septentrio-gnss/mowi/3Doutput/png_renders/mowi_angle_2.png

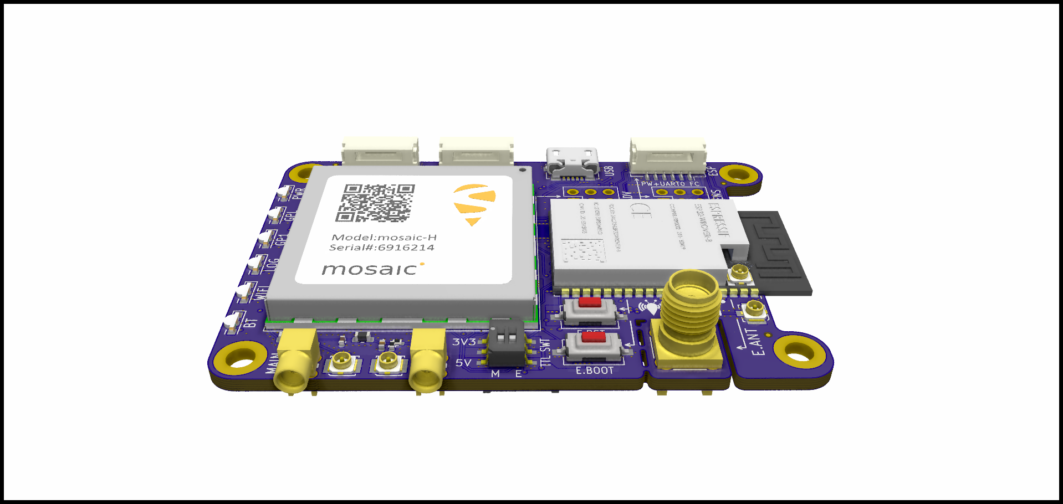
3Doutput/png_renders/mowi_angle_2.png
