septentrio-gnss/mowi/3Doutput/png_renders/mowi_angle_3.png

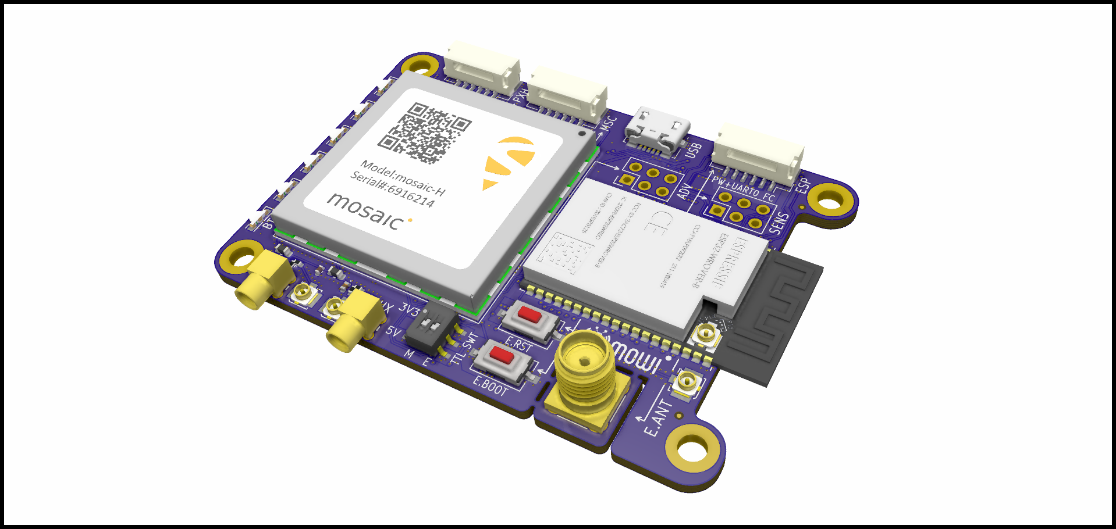
3Doutput/png_renders/mowi_angle_3.png
