septentrio-gnss/mowi/3Doutput/png_renders/mowi_angle_4.png

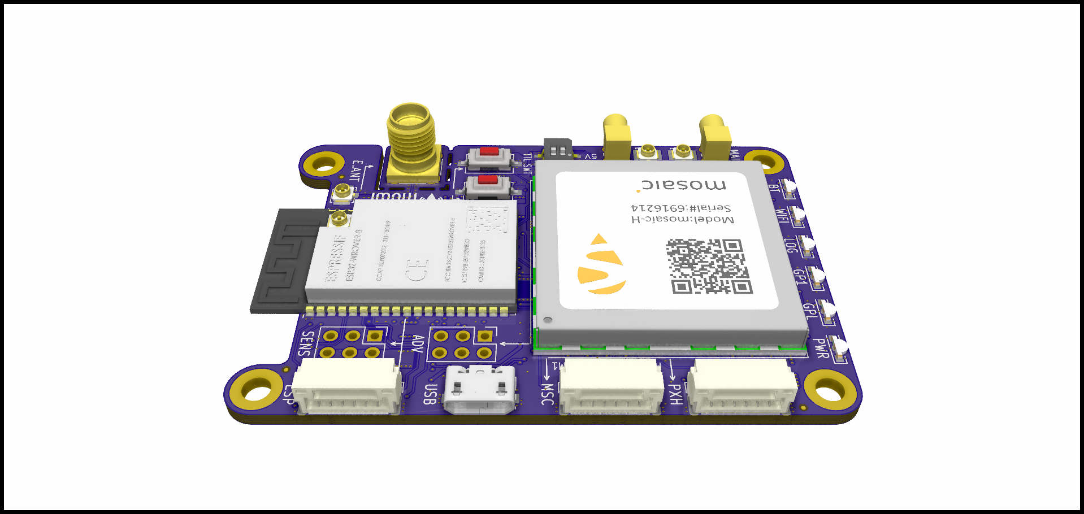
3Doutput/png_renders/mowi_angle_4.png
