septentrio-gnss/mowi/3Doutput/png_renders/mowi_bottom.png

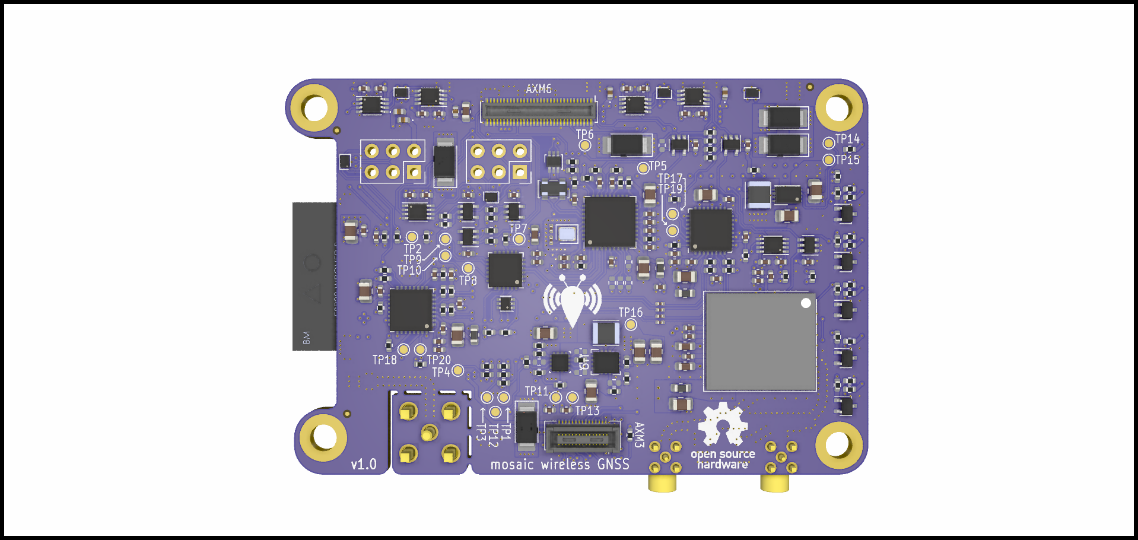
3Doutput/png_renders/mowi_bottom.png
