septentrio-gnss/mowi/readmeSource/examples_wifi_client_networks.png

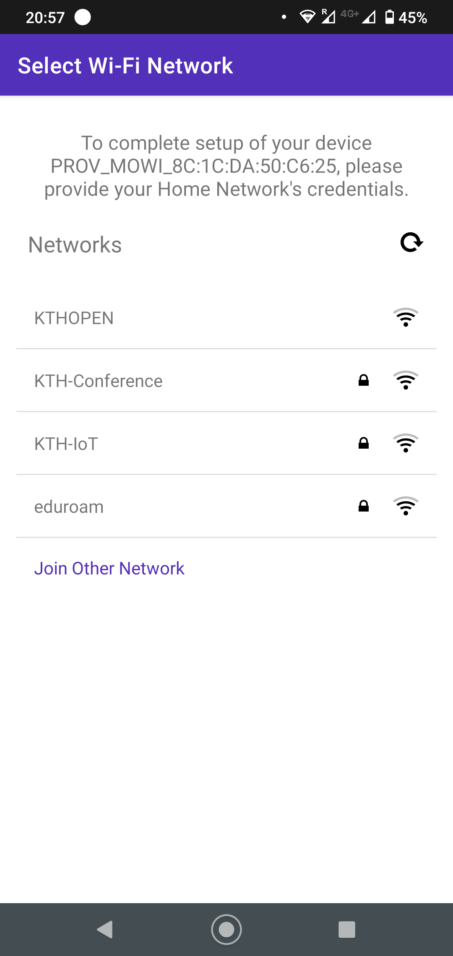
readmeSource/examples_wifi_client_networks.png
