septentrio-gnss/mowi/readmeSource/examples_wifi_client_search.png

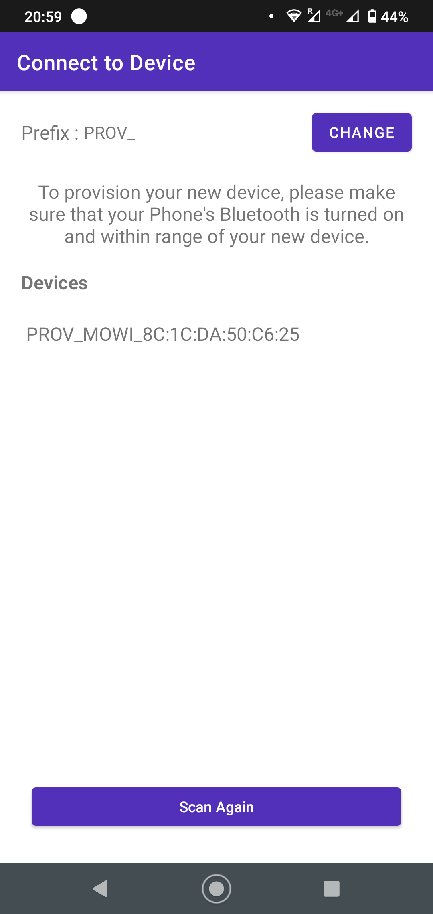
readmeSource/examples_wifi_client_search.png
