septentrio-gnss/mowi/readmeSource/mowi_3Drender_angle_3.png

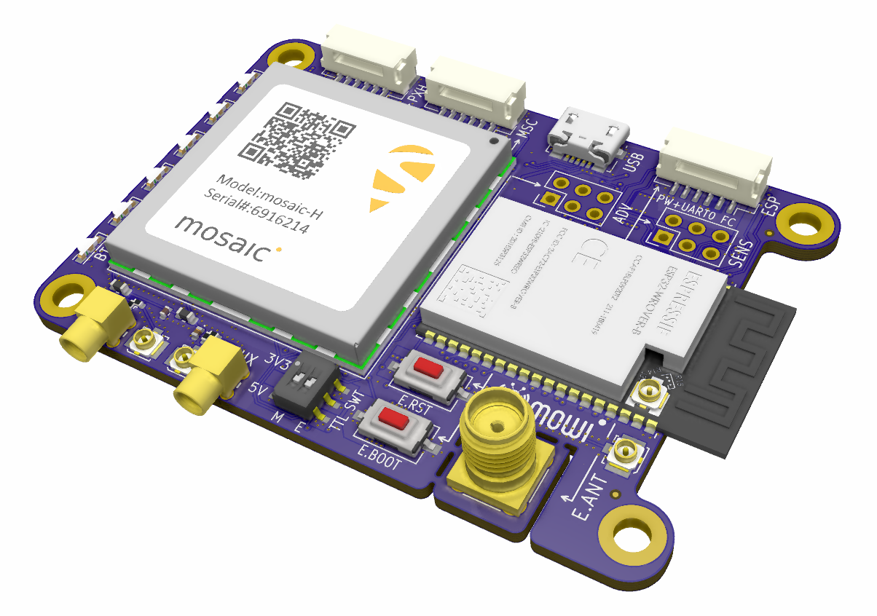
readmeSource/mowi_3Drender_angle_3.png
