septentrio-gnss/mowi/readmeSource/phone_mockup.png

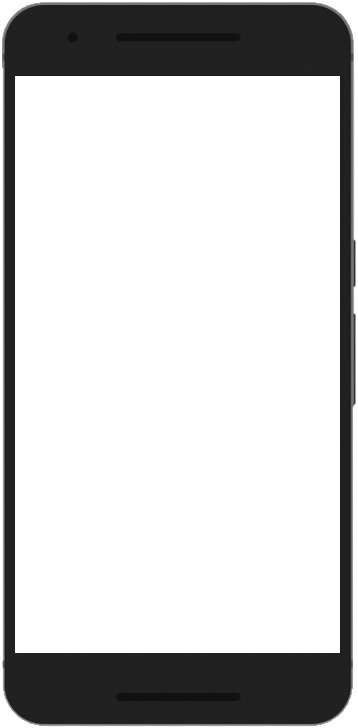
readmeSource/phone_mockup.png
