septentrio-gnss/mowi/mowi/mowi.sch

## KiCad design mowi/mowi.sch (2024-07-09)

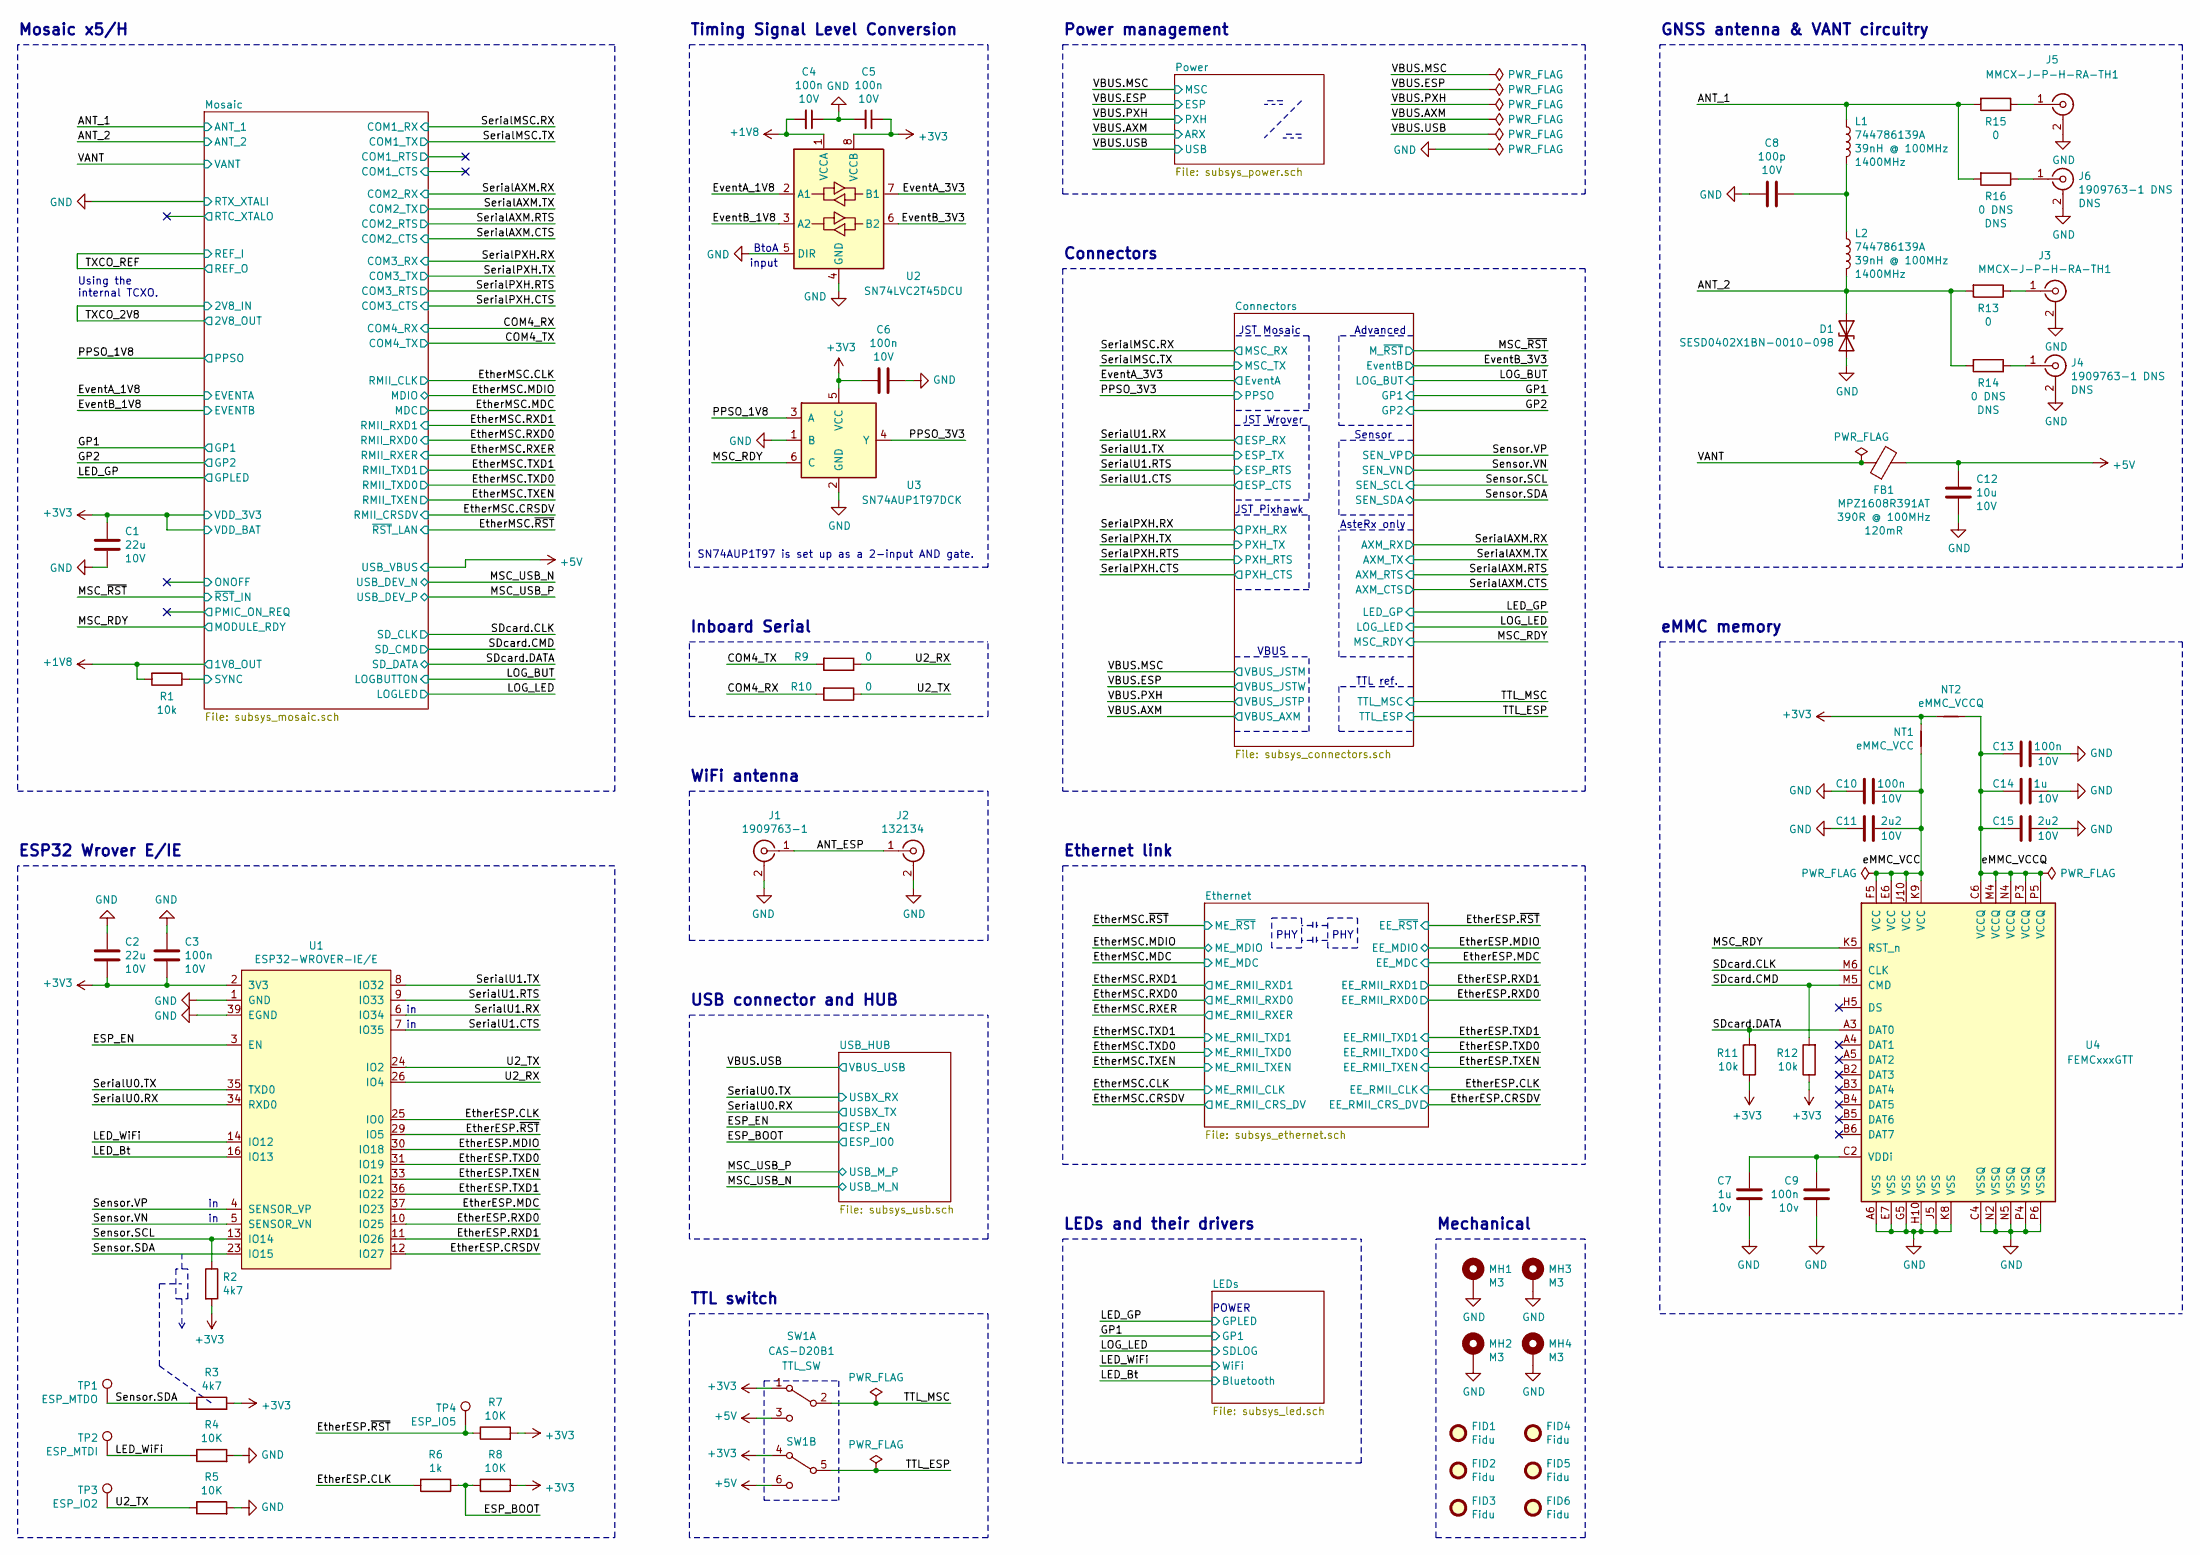
[picture p45: schematic mowi.sch]

Parts:
C1, C2: 22u; C_0805_2012Metric; Voltage 10V
C3, C4, C5, C6, C10, C13: 100n; C_0402_1005Metric; Voltage 10V
C7: 1u; C_0402_1005Metric; Voltage 10v
C8: 100p; C_0402_1005Metric; Voltage 10V
C9: 100n; C_0402_1005Metric; Voltage 10v
C11, C15: 2u2; C_0603_1608Metric; Voltage 10V
C12: 10u; C_0805_2012Metric; Voltage 10V
C14: 1u; C_0402_1005Metric; Voltage 10V
D1: SESD0402X1BN-0010-098; D_0402_1005Metric
FB1: MPZ1608R391AT; L_0603_1608Metric
FID1, FID2, FID3, FID4, FID5, FID6: Fidu; Fiducial_0.5mm_Mask1mm
J1: 1909763-1; TE_1909763-1
J2: 132134; SMA_Amphenol_132134-16_Vertical
J3, J5: MMCX-J-P-H-RA-TH1; Samtec_MMCX-J-P-H-RA-TH1
J4, J6: 1909763-1 DNS; TE_1909763-1
L1, L2: 744786139A; L_0603_1608Metric
MH1, MH2, MH3, MH4: M3; MountingHole_3.2mm_M3_ISO7380_Pad
NT1: eMMC_VCC; NetTie-2_SMD_Pad0.5mm
NT2: eMMC_VCCQ; NetTie-2_SMD_Pad0.5mm
R1, R11, R12: 10k; R_0402_1005Metric
R2, R3: 4k7; R_0402_1005Metric
R4, R5, R7, R8: 10K; R_0402_1005Metric
R6: 1k; R_0402_1005Metric
R9, R10, R13, R15: 0; R_0402_1005Metric
R14, R16: 0 DNS; R_0402_1005Metric
SW1: CAS-D20B1; SW_DIP_SPDTx02_CAS_CAS-D20B1_5.4x3.9x2.5mm
TP1: ESP_MTDO; TestPoint_Pad_D1.0mm
TP2: ESP_MTDI; TestPoint_Pad_D1.0mm
TP3: ESP_IO2; TestPoint_Pad_D1.0mm
TP4: ESP_IO5; TestPoint_Pad_D1.0mm
U1: ESP32-WROVER-IE/E; Esp_ESP32-WROVER-(I)E_18.0x31.4x3.3mm
U2: SN74LVC2T45DCU; VSSOP-8_2.3x2mm_P0.5mm
U3: SN74AUP1T97DCK; SOT-363_SC-70-6
U4: FEMCxxxGTT; FBGA-153_13.0x11.5x1.0mm

Connections:
+1V8: C4.2, R1.2, U2.1 (VCCA)
+3V3: C1.2, C2.2, C3.2, C5.1, C6.2, NT1.1, NT2.1, R2.2, R3.2, R7.2, R8.2, R11.1, R12.1, SW1.1 (A), SW1.4 (A), U1.2 (3V3), U2.8 (VCCB), U3.5 (VCC)
+5V: C12.2, FB1.2, SW1.3 (C), SW1.6 (C)
ANT_1: L1.1, R15.2, R16.2
ANT_2: D1.1 (A1), L2.2, R13.2, R14.2
ANT_ESP: J1.1 (In), J2.1 (In)
COM4_RX: R10.2
COM4_TX: R9.2
ESP_BOOT: R6.1, R8.1
ESP_EN: U1.3 (EN)
EtherESP.CLK: R6.2, U1.25 (IO0)
EtherESP.CRSDV: U1.12 (IO27)
EtherESP.MDC: U1.37 (IO23)
EtherESP.MDIO: U1.30 (IO18)
EtherESP.RXD0: U1.10 (IO25)
EtherESP.RXD1: U1.11 (IO26)
EtherESP.TXD0: U1.31 (IO19)
EtherESP.TXD1: U1.36 (IO22)
EtherESP.TXEN: U1.33 (IO21)
EtherESP.~RST: R7.1, TP4.1, U1.29 (IO5)
EventA_1V8: U2.2 (A1)
EventA_3V3: U2.7 (B1)
EventB_1V8: U2.3 (A2)
EventB_3V3: U2.6 (B2)
GND: C1.1, C2.1, C3.1, C4.1, C5.2, C6.1, C7.2, C8.2, C9.2, C10.2, C11.2, C12.1, C13.2, C14.2, C15.2, D1.2 (A2), J1.2 (Ext), J2.2 (Ext), J3.2 (Ext), J4.2 (Ext), J5.2 (Ext), J6.2 (Ext), MH1.1, MH2.1, MH3.1, MH4.1, R4.2, R5.2, U1.1 (GND), U1.15 (GND), U1.38 (GND), U1.39 (EGND), U2.4 (GND), U2.5 (DIR), U3.1 (B), U3.2 (GND), U4.A6 (VSS), U4.C4 (VSSQ), U4.E7 (VSS), U4.G5 (VSS), U4.H10 (VSS), U4.J5 (VSS), U4.K8 (VSS), U4.N2 (VSSQ), U4.N5 (VSSQ), U4.P4 (VSSQ), U4.P6 (VSSQ)
LED_Bt: U1.16 (IO13)
LED_WiFi: R4.1, TP2.1, U1.14 (IO12)
MSC_RDY: U3.6 (C), U4.K5 (RST_n)
unnamed: C7.1, C9.1, U4.C2 (VDDi)
unnamed: C8.1, L1.2, L2.1
unnamed: J3.1 (In), R13.1
unnamed: J4.1 (In), R14.1
unnamed: J5.1 (In), R15.1
unnamed: J6.1 (In), R16.1
PPSO_1V8: U3.3 (A)
PPSO_3V3: U3.4 (Y)
SDcard.CLK: U4.M6 (CLK)
SDcard.CMD: R12.2, U4.M5 (CMD)
SDcard.DATA: R11.2, U4.A3 (DAT0)
SYNC: R1.1
Sensor.SCL: R2.1, U1.13 (IO14)
Sensor.SDA: R3.1, TP1.1, U1.23 (IO15)
Sensor.VN: U1.5 (SENSOR_VN)
Sensor.VP: U1.4 (SENSOR_VP)
SerialU0.RX: U1.34 (RXD0)
SerialU0.TX: U1.35 (TXD0)
SerialU1.CTS: U1.7 (IO35)
SerialU1.RTS: U1.9 (IO33)
SerialU1.RX: U1.6 (IO34)
SerialU1.TX: U1.8 (IO32)
TTL_ESP: SW1.5 (B)
TTL_MSC: SW1.2 (B)
U2_RX: R9.1, U1.26 (IO4)
U2_TX: R5.1, R10.1, TP3.1, U1.24 (IO2)
VANT: FB1.1
eMMC_VCC: C10.1, C11.1, NT1.2, U4.E6 (VCC), U4.F5 (VCC), U4.J10 (VCC), U4.K9 (VCC)
eMMC_VCCQ: C13.1, C14.1, C15.1, NT2.2, U4.C6 (VCCQ), U4.M4 (VCCQ), U4.N4 (VCCQ), U4.P3 (VCCQ), U4.P5 (VCCQ)

Notes on the sheet:
ESP32 Wrover E/IE
TTL switch
GNSS antenna & VANT circuitry
POWER
LEDs and their drivers
Mechanical
Using the internal TCXO.
Mosaic x5/H
eMMC memory
BtoA
input
USB connector and HUB
SN74AUP1T97 is set up as a 2-input AND gate.
Timing Signal Level Conversion
Inboard Serial
Power management
AsteRx only
TTL ref.
Sensor
JST Pixhawk
JST Wrover
VBUS
Advanced
JST Mosaic
Connectors
PHY
Ethernet link
WiFi antenna
