septentrio-gnss/mowi/mowi/subsys_connectors.sch

## KiCad design mowi/subsys_connectors.sch (2021-09-02)

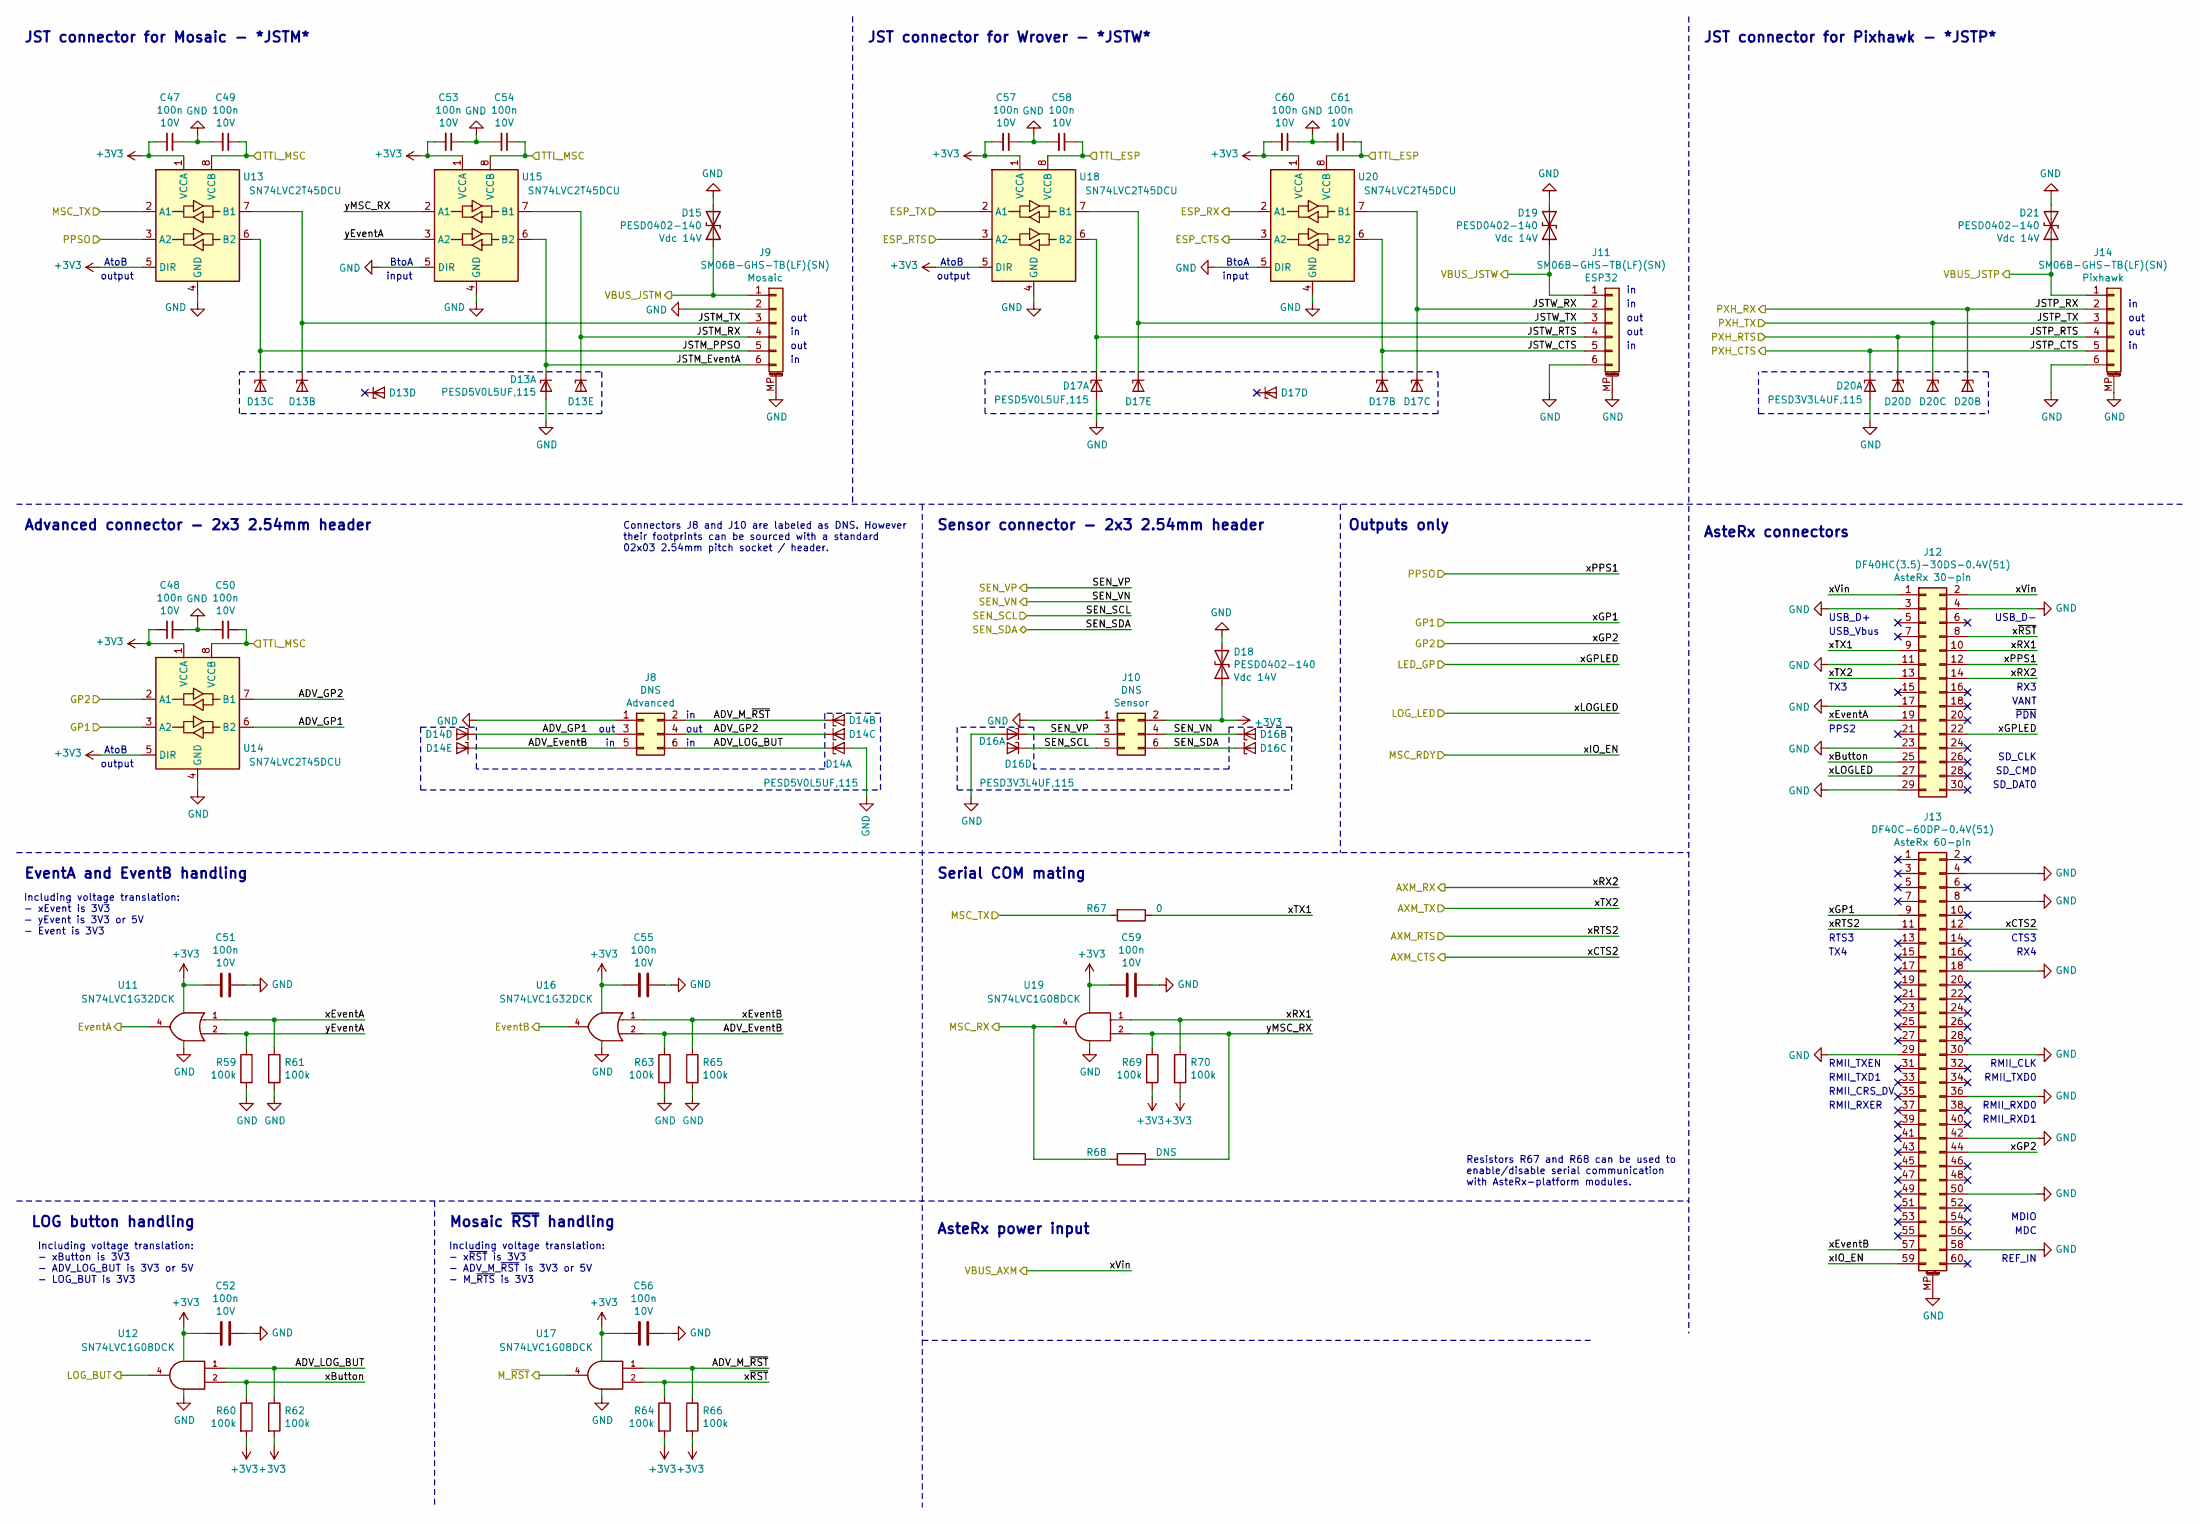
[picture p46: schematic subsys_connectors.sch]

Parts:
C47, C48, C49, C50, C51, C52, C53, C54, C55, C56, C57, C58, C59, C60, C61: 100n; C_0402_1005Metric; Voltage 10V
D13, D14, D17: PESD5V0L5UF,115; SOT-886
D15, D18, D19, D21: PESD0402-140; D_0402_1005Metric
D16, D20: PESD3V3L4UF,115; SOT-886
J8, J10: DNS; PinHeader_2x03_P2.54mm
J9, J11, J14: SM06B-GHS-TB(LF)(SN); JST_GH_SM06B-GHS-TB_1x06-1MP_P1.25mm_Horizontal
J12: DF40HC(3.5)-30DS-0.4V(51); Hirose_DF40HC-30DS-0.4V(51)
J13: DF40C-60DP-0.4V(51); Hirose_DF40C-60DP-0.4V(51)
R59, R60, R61, R62, R63, R64, R65, R66, R69, R70: 100k; R_0402_1005Metric
R67: 0; R_0402_1005Metric
R68: DNS; R_0402_1005Metric
U11, U16: SN74LVC1G32DCK; SOT-353_SC-70-5
U12, U17, U19: SN74LVC1G08DCK; SOT-353_SC-70-5
U13, U14, U15, U18, U20: SN74LVC2T45DCU; VSSOP-8_2.3x2mm_P0.5mm

Connections:
+3V3: C47.2, C48.2, C51.2, C52.2, C53.2, C55.2, C56.2, C57.2, C59.2, C60.2, D18.1 (A1), J10.2, R60.2, R62.2, R64.2, R66.2, R69.2, R70.2, U11.5 (VCC), U12.5 (VCC), U13.1 (VCCA), U13.5 (DIR), U14.1 (VCCA), U14.5 (DIR), U15.1 (VCCA), U16.5 (VCC), U17.5 (VCC), U18.1 (VCCA), U18.5 (DIR), U19.5 (VCC), U20.1 (VCCA)
ADV_EventB: D14.6 (K5), J8.5, R63.1, U16.2
ADV_GP1: D14.5 (K4), J8.3, U14.6 (B2)
ADV_GP2: D14.4 (K3), J8.4, U14.7 (B1)
ADV_LOG_BUT: D14.1 (K1), J8.6, R62.1, U12.1
ADV_M_~RST: D14.3 (K2), J8.2, R66.1, U17.1
AXM_CTS: J13.12
AXM_RTS: J13.11
AXM_RX: J12.14
AXM_TX: J12.13
ESP_CTS: U20.3 (A2)
ESP_RTS: U18.3 (A2)
ESP_RX: U20.2 (A1)
ESP_TX: U18.2 (A1)
EventA: U11.4
EventB: U16.4
GND: C47.1, C48.1, C49.2, C50.2, C51.1, C52.1, C53.1, C54.2, C55.1, C56.1, C57.1, C58.2, C59.1, C60.1, C61.2, D13.2 (A), D14.2 (A), D15.2 (A2), D16.2 (A), D16.5 (A), D17.2 (A), D18.2 (A2), D19.2 (A2), D20.2 (A), D20.5 (A), D21.2 (A2), J8.1, J9.2, J9.MP (MountPin), J10.1, J11.6, J11.MP (MountPin), J12.3, J12.4, J12.11, J12.17, J12.23, J12.29, J13.4, J13.8, J13.18, J13.29, J13.30, J13.36, J13.42, J13.50, J13.58, J13.MP (MountPin), J14.6, J14.MP (MountPin), R59.2, R61.2, R63.2, R65.2, U11.3 (GND), U12.3 (GND), U13.4 (GND), U14.4 (GND), U15.4 (GND), U15.5 (DIR), U16.3 (GND), U17.3 (GND), U18.4 (GND), U19.3 (GND), U20.4 (GND), U20.5 (DIR)
GP1: J13.9, U14.3 (A2)
GP2: J13.44, U14.2 (A1)
JSTM_EventA: D13.1 (K1), J9.6, U15.6 (B2)
JSTM_PPSO: D13.4 (K3), J9.5, U13.6 (B2)
JSTM_RX: D13.6 (K5), J9.4, U15.7 (B1)
JSTM_TX: D13.3 (K2), J9.3, U13.7 (B1)
JSTP_CTS: D20.1 (K1), J14.5
JSTP_RTS: D20.6 (K4), J14.4
JSTP_RX: D20.3 (K2), J14.2
JSTP_TX: D20.4 (K3), J14.3
JSTW_CTS: D17.3 (K2), J11.5, U20.6 (B2)
JSTW_RTS: D17.1 (K1), J11.4, U18.6 (B2)
JSTW_RX: D17.4 (K3), J11.2, U20.7 (B1)
JSTW_TX: D17.6 (K5), J11.3, U18.7 (B1)
LED_GP: J12.22
LOG_BUT: U12.4
LOG_LED: J12.27
MSC_RDY: J13.59
MSC_RX: R68.2, U19.4
MSC_TX: R67.2, U13.2 (A1)
M_~RST: U17.4
PPSO: J12.12, U13.3 (A2)
SEN_SCL: D16.6 (K4), J10.5
SEN_SDA: D16.4 (K3), J10.6
SEN_VN: D16.3 (K2), J10.4
SEN_VP: D16.1 (K1), J10.3
TTL_ESP: C58.1, C61.1, U18.8 (VCCB), U20.8 (VCCB)
TTL_MSC: C49.1, C50.1, C54.1, U13.8 (VCCB), U14.8 (VCCB), U15.8 (VCCB)
VBUS_AXM: J12.1, J12.2
VBUS_JSTM: D15.1 (A1), J9.1
VBUS_JSTP: D21.1 (A1), J14.1
VBUS_JSTW: D19.1 (A1), J11.1
xButton: J12.25, R60.1, U12.2
xEventA: J12.19, R61.1, U11.1
xEventB: J13.57, R65.1, U16.1
xRX1: J12.10, R70.1, U19.1
xTX1: J12.9, R67.1
x~RST: J12.8, R64.1, U17.2
yEventA: R59.1, U11.2, U15.3 (A2)
yMSC_RX: R68.1, R69.1, U15.2 (A1), U19.2

Notes on the sheet:
input
output
AtoB
BtoA
JST connector for Mosaic - *JSTM*
JST connector for Wrover - *JSTW*
JST connector for Pixhawk - *JSTP*
Advanced connector - 2x3 2.54mm header
out
Sensor connector - 2x3 2.54mm header
USB_D+
USB_Vbus
USB_D-
PPS2
SD_CLK
SD_CMD
SD_DAT0
RMII_TXEN
RMII_TXD1
RMII_CRS_DV
RMII_RXER
RMII_CLK
RMII_TXD0
RMII_RXD0
RMII_RXD1
MDIO
MDC
AsteRx connectors
REF_IN
~PDN
TX4
RX4
RTS3
CTS3
TX3
RX3
EventA and EventB handling
LOG button handling
Outputs only
Serial COM mating
Mosaic ~RST~ handling
Including voltage translation: - xEvent is 3V3 - yEvent is 3V3 or 5V - Event is 3V3
AsteRx power input
VANT
Including voltage translation: - x~RST~ is 3V3 - ADV_M_~RST~ is 3V3 or 5V - M_~RTS~ is 3V3
Including voltage translation: - xButton is 3V3 - ADV_LOG_BUT is 3V3 or 5V - LOG_BUT is 3V3
Resistors R67 and R68 can be used to enable/disable serial communication with AsteRx-platform modules.
Connectors J8 and J10 are labeled as DNS. However their footprints can be sourced with a standard 02x03 2.54mm pitch socket / header.
