septentrio-gnss/mowi/mowi/subsys_ethernet.sch

## KiCad design mowi/subsys_ethernet.sch (2021-09-02)

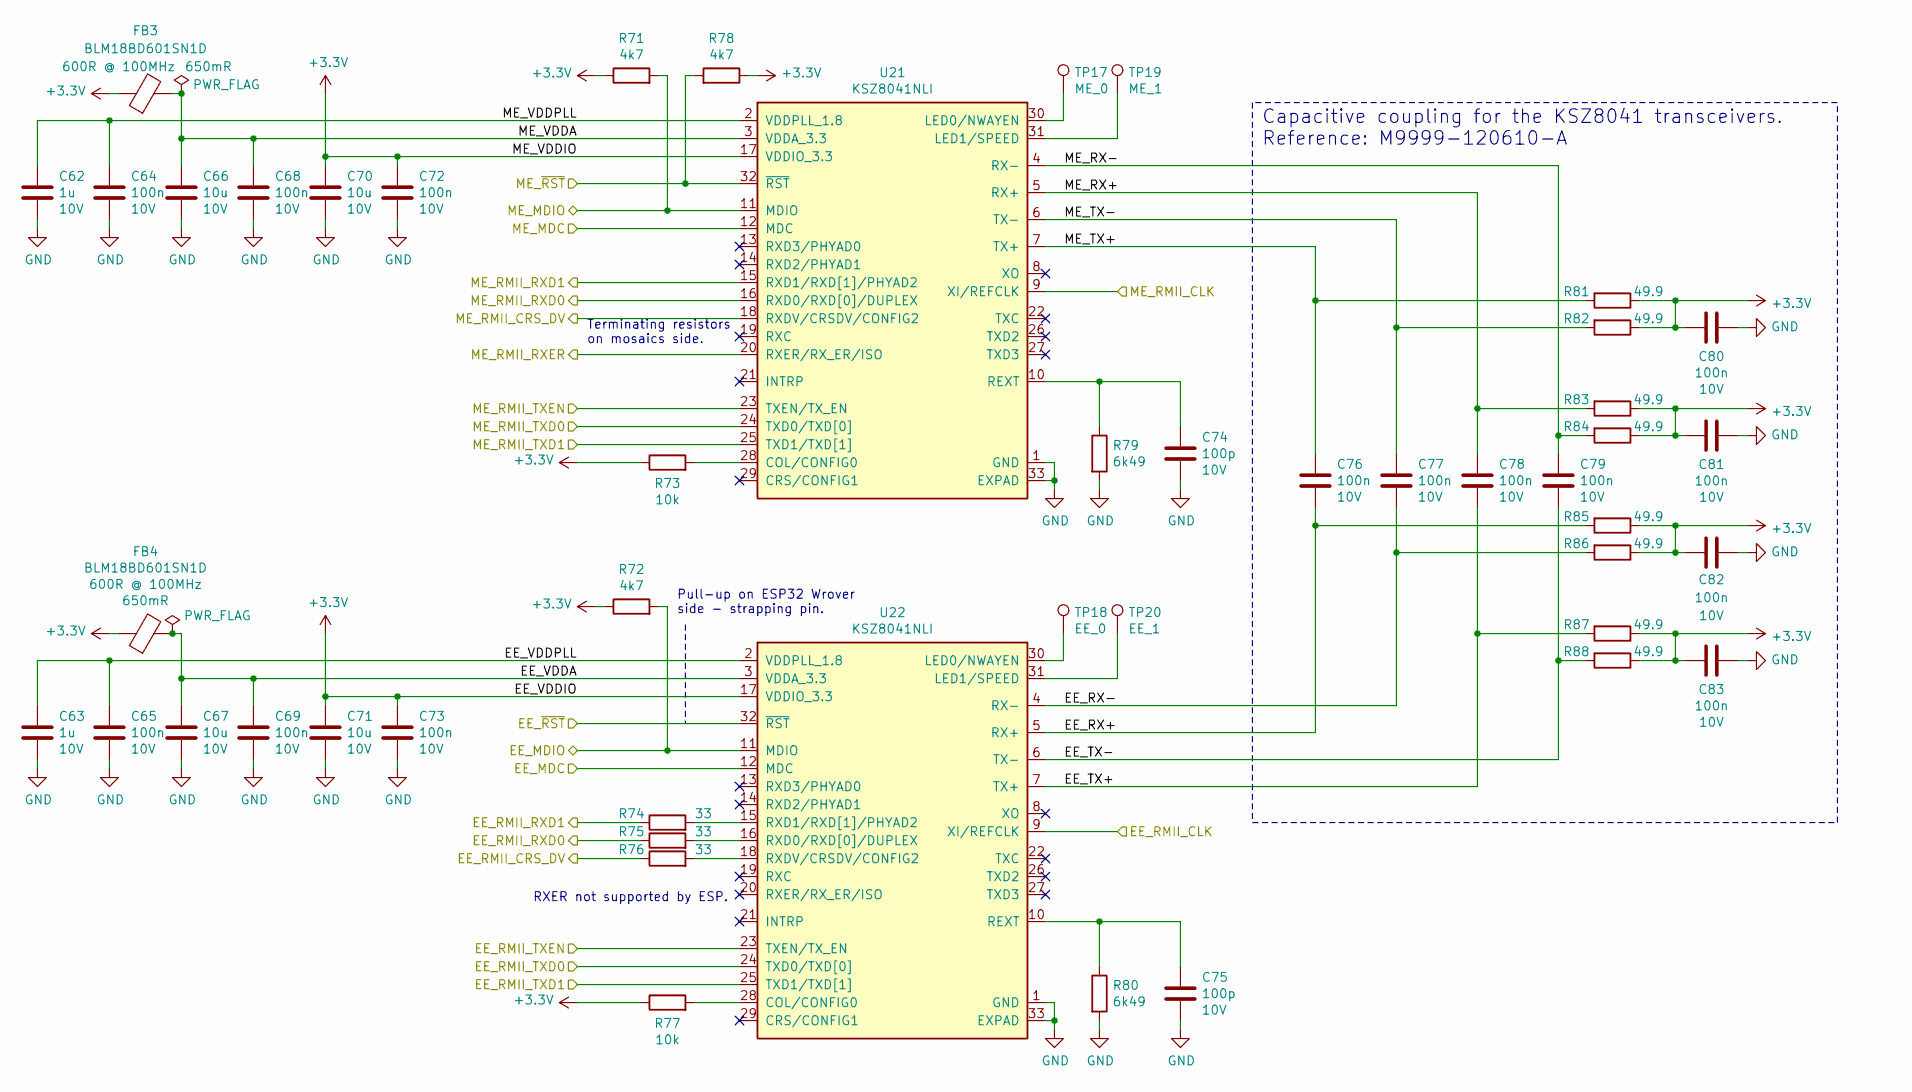
[picture p47: schematic subsys_ethernet.sch]

Parts:
C62, C63: 1u; C_0402_1005Metric; Voltage 10V
C64, C65, C68, C69, C72, C73, C80, C81, C82, C83: 100n; C_0402_1005Metric; Voltage 10V
C66, C67, C70, C71: 10u; C_0805_2012Metric; Voltage 10V
C74, C75: 100p; C_0402_1005Metric; Voltage 10V
C76, C77, C78, C79: 100n; C_0201_0603Metric; Voltage 10V
FB3, FB4: BLM18BD601SN1D; L_0603_1608Metric
R71, R72, R78: 4k7; R_0402_1005Metric
R73, R77: 10k; R_0402_1005Metric
R74, R75, R76: 33; R_0402_1005Metric
R79, R80: 6k49; R_0402_1005Metric
R81, R82, R83, R84, R85, R86, R87, R88: 49.9; R_0402_1005Metric
TP17: ME_0; TestPoint_Pad_D1.0mm
TP18: EE_0; TestPoint_Pad_D1.0mm
TP19: ME_1; TestPoint_Pad_D1.0mm
TP20: EE_1; TestPoint_Pad_D1.0mm
U21, U22: KSZ8041NLI; QFN-32-1EP_5x5mm_P0.5mm_EP3.3x3.3mm_ThermalVias

Connections:
+3.3V: C70.1, C71.1, C72.1, C73.1, C80.2, C81.2, C82.2, C83.2, FB3.1, FB4.1, R71.1, R72.1, R73.1, R77.1, R78.1, R81.1, R82.1, R83.1, R84.1, R85.1, R86.1, R87.1, R88.1, U21.17 (VDDIO_3.3), U22.17 (VDDIO_3.3)
EE_MDC: U22.12 (MDC)
EE_MDIO: R72.2, U22.11 (MDIO)
EE_RMII_CLK: U22.9 (XI/REFCLK)
EE_RMII_CRS_DV: R76.1
EE_RMII_RXD0: R75.1
EE_RMII_RXD1: R74.1
EE_RMII_TXD0: U22.24 (TXD0/TXD[0])
EE_RMII_TXD1: U22.25 (TXD1/TXD[1])
EE_RMII_TXEN: U22.23 (TXEN/TX_EN)
EE_RX+: C76.2, R85.2, U22.5 (RX+)
EE_RX-: C77.2, R86.2, U22.4 (RX-)
EE_TX+: C78.2, R87.2, U22.7 (TX+)
EE_TX-: C79.2, R88.2, U22.6 (TX-)
EE_VDDA: C67.1, C69.1, FB4.2, U22.3 (VDDA_3.3)
EE_VDDPLL: C63.1, C65.1, U22.2 (VDDPLL_1.8)
EE_~RST: U22.32 (~RST)
GND: C62.2, C63.2, C64.2, C65.2, C66.2, C67.2, C68.2, C69.2, C70.2, C71.2, C72.2, C73.2, C74.2, C75.2, C80.1, C81.1, C82.1, C83.1, R79.2, R80.2, U21.1 (GND), U21.33 (EXPAD), U22.1 (GND), U22.33 (EXPAD)
ME_MDC: U21.12 (MDC)
ME_MDIO: R71.2, U21.11 (MDIO)
ME_RMII_CLK: U21.9 (XI/REFCLK)
ME_RMII_CRS_DV: U21.18 (RXDV/CRSDV/CONFIG2)
ME_RMII_RXD0: U21.16 (RXD0/RXD[0]/DUPLEX)
ME_RMII_RXD1: U21.15 (RXD1/RXD[1]/PHYAD2)
ME_RMII_RXER: U21.20 (RXER/RX_ER/ISO)
ME_RMII_TXD0: U21.24 (TXD0/TXD[0])
ME_RMII_TXD1: U21.25 (TXD1/TXD[1])
ME_RMII_TXEN: U21.23 (TXEN/TX_EN)
ME_RX+: C78.1, R83.2, U21.5 (RX+)
ME_RX-: C79.1, R84.2, U21.4 (RX-)
ME_TX+: C76.1, R81.2, U21.7 (TX+)
ME_TX-: C77.1, R82.2, U21.6 (TX-)
ME_VDDA: C66.1, C68.1, FB3.2, U21.3 (VDDA_3.3)
ME_VDDPLL: C62.1, C64.1, U21.2 (VDDPLL_1.8)
ME_~RST: R78.2, U21.32 (~RST)
unnamed: C74.1, R79.1, U21.10 (REXT)
unnamed: C75.1, R80.1, U22.10 (REXT)
unnamed: R73.2, U21.28 (COL/CONFIG0)
unnamed: R74.2, U22.15 (RXD1/RXD[1]/PHYAD2)
unnamed: R75.2, U22.16 (RXD0/RXD[0]/DUPLEX)
unnamed: R76.2, U22.18 (RXDV/CRSDV/CONFIG2)
unnamed: R77.2, U22.28 (COL/CONFIG0)
unnamed: TP17.1, U21.30 (LED0/NWAYEN)
unnamed: TP18.1, U22.30 (LED0/NWAYEN)
unnamed: TP19.1, U21.31 (LED1/SPEED)
unnamed: TP20.1, U22.31 (LED1/SPEED)

Notes on the sheet:
Capacitive coupling for the KSZ8041 transceivers. Reference: M9999-120610-A
Pull-up on ESP32 Wrover side - strapping pin.
RXER not supported by ESP.
Terminating resistors on mosaics side.
