septentrio-gnss/mowi/mowi/subsys_led.sch

## KiCad design mowi/subsys_led.sch (2021-09-02)

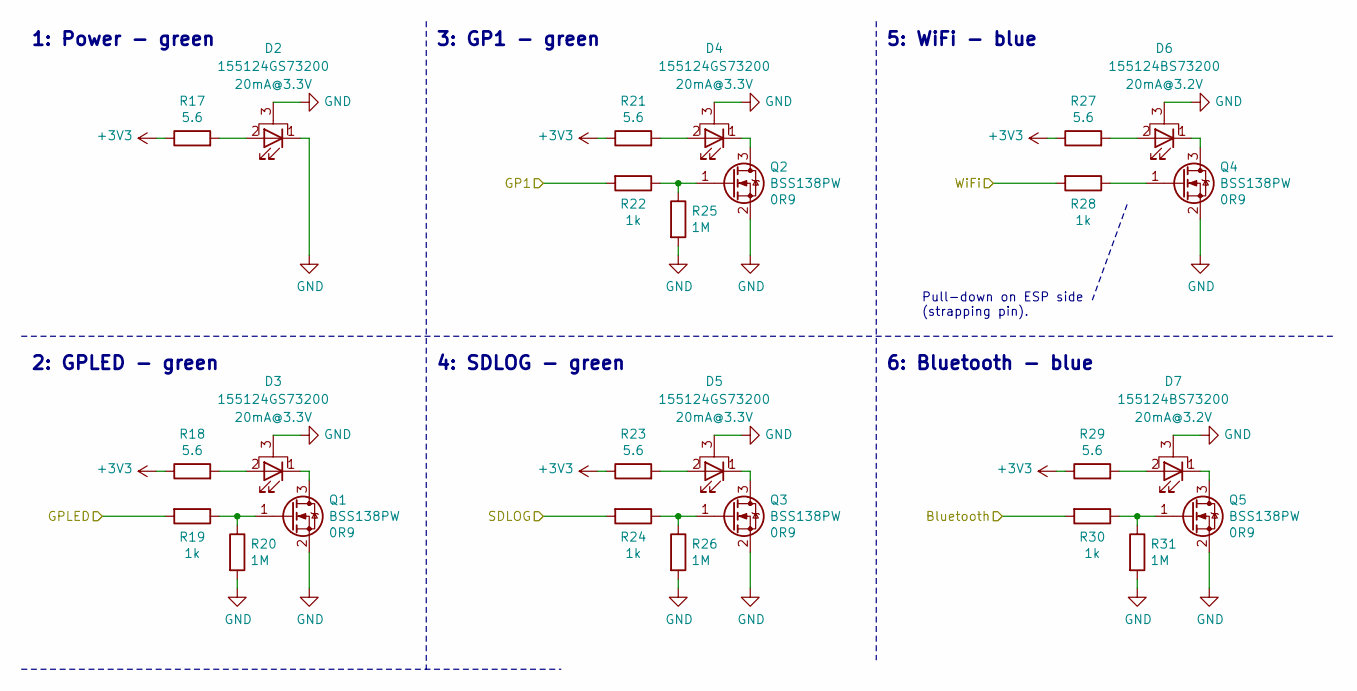
[picture p48: schematic subsys_led.sch]

Parts:
D2, D3, D4, D5: 155124GS73200; LED_Wuerth_WL-SMSW-1204
D6, D7: 155124BS73200; LED_Wuerth_WL-SMSW-1204
Q1, Q2, Q3, Q4, Q5: BSS138PW; SOT-323_SC-70
R17, R18, R21, R23, R27, R29: 5.6; R_0402_1005Metric
R19, R22, R24, R28, R30: 1k; R_0402_1005Metric
R20, R25, R26, R31: 1M; R_0402_1005Metric

Connections:
+3V3: R17.1, R18.1, R21.1, R23.1, R27.1, R29.1
Bluetooth: R30.2
GND: D2.1 (K), D2.3 (PAD), D3.3 (PAD), D4.3 (PAD), D5.3 (PAD), D6.3 (PAD), D7.3 (PAD), Q1.2 (S), Q2.2 (S), Q3.2 (S), Q4.2 (S), Q5.2 (S), R20.2, R25.2, R26.2, R31.2
GP1: R22.2
GPLED: R19.2
unnamed: D2.2 (A), R17.2
unnamed: D3.1 (K), Q1.3 (D)
unnamed: D3.2 (A), R18.2
unnamed: D4.1 (K), Q2.3 (D)
unnamed: D4.2 (A), R21.2
unnamed: D5.1 (K), Q3.3 (D)
unnamed: D5.2 (A), R23.2
unnamed: D6.1 (K), Q4.3 (D)
unnamed: D6.2 (A), R27.2
unnamed: D7.1 (K), Q5.3 (D)
unnamed: D7.2 (A), R29.2
unnamed: Q1.1 (G), R19.1, R20.1
unnamed: Q2.1 (G), R22.1, R25.1
unnamed: Q3.1 (G), R24.1, R26.1
unnamed: Q4.1 (G), R28.1
unnamed: Q5.1 (G), R30.1, R31.1
SDLOG: R24.2
WiFi: R28.2

Notes on the sheet:
6: Bluetooth - blue
5: WiFi - blue
3: GP1 - green
1: Power - green
2: GPLED - green
4: SDLOG - green
Pull-down on ESP side (strapping pin).
