septentrio-gnss/mowi/mowi/subsys_power.sch

## KiCad design mowi/subsys_power.sch (2021-09-17)

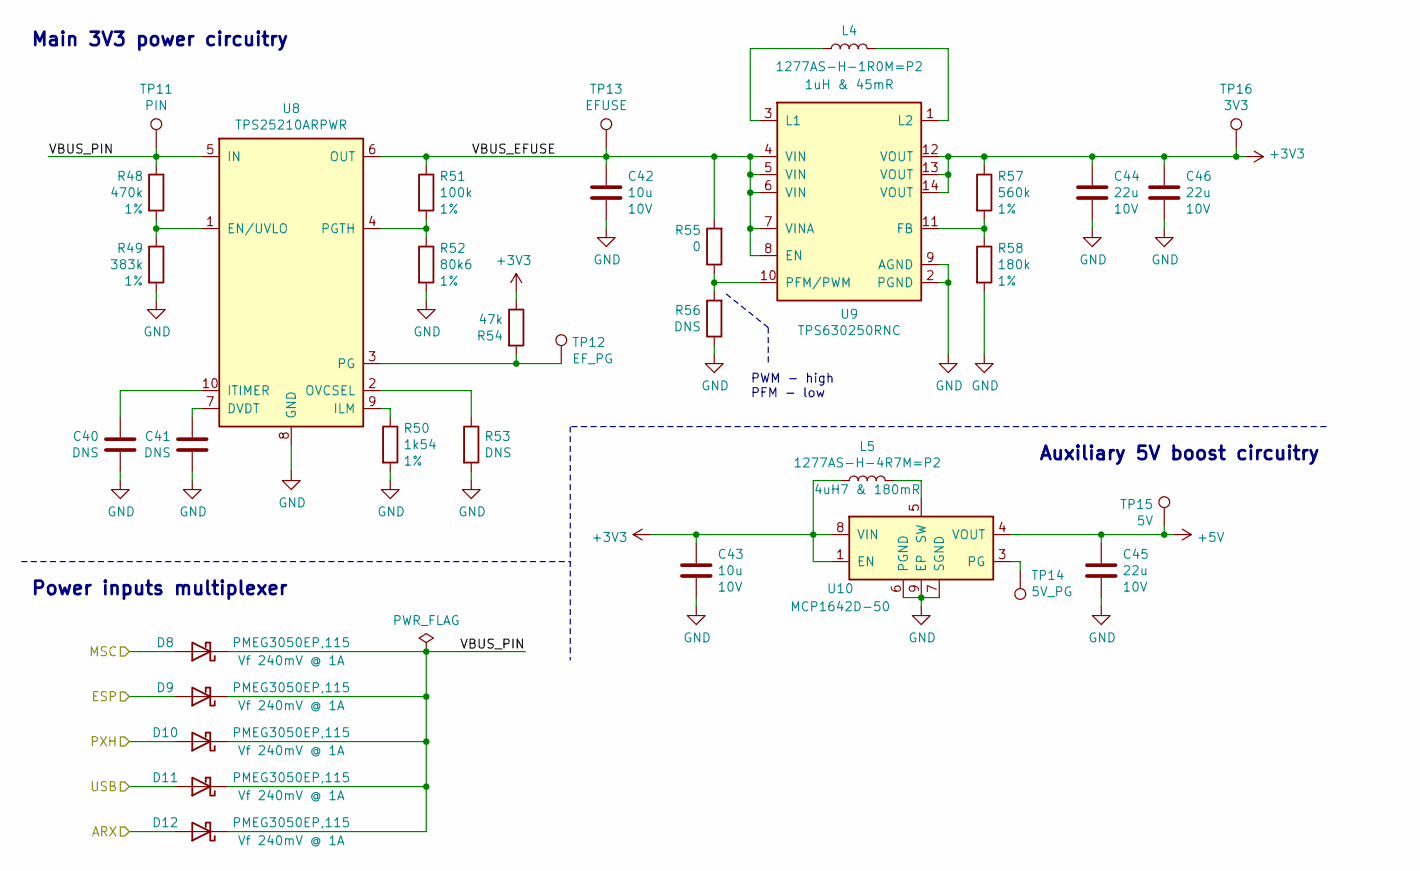
[picture p49: schematic subsys_power.sch]

Parts:
C40, C41: DNS; C_0402_1005Metric
C42: 10u; C_0805_2012Metric
C43: 10u; C_0805_2012Metric; Voltage 10V
C44, C45, C46: 22u; C_0805_2012Metric
D8, D9, D10, D11, D12: PMEG3050EP,115; D_SOD-128
L4: 1277AS-H-1R0M=P2; L_Murata_DFE322512C_3.2x2.5x1.2mm
L5: 1277AS-H-4R7M=P2; L_Murata_DFE322512C_3.2x2.5x1.2mm
R48: 470k; R_0402_1005Metric; Tolerance 1%
R49: 383k; R_0402_1005Metric; Tolerance 1%
R50: 1k54; R_0402_1005Metric; Tolerance 1%
R51: 100k; R_0402_1005Metric; Tolerance 1%
R52: 80k6; R_0402_1005Metric; Tolerance 1%
R53, R56: DNS; R_0402_1005Metric
R54: 47k; R_0402_1005Metric
R55: 0; R_0402_1005Metric
R57: 560k; R_0402_1005Metric; Tolerance 1%
R58: 180k; R_0402_1005Metric; Tolerance 1%
TP11: PIN; TestPoint_Pad_D1.0mm
TP12: EF_PG; TestPoint_Pad_D1.0mm
TP13: EFUSE; TestPoint_Pad_D1.0mm
TP14: 5V_PG; TestPoint_Pad_D1.0mm
TP15: 5V; TestPoint_Pad_D1.0mm
TP16: 3V3; TestPoint_Pad_D1.0mm
U8: TPS25210ARPWR; Texas_VQFN-HR-10_2.0x2.0x1.0mm
U9: TPS630250RNC; Texas_VQFN-HR-14_3.0x2.5x1.0mm
U10: MCP1642D-50; DFN-8-1EP_3x2mm_P0.5mm_EP1.75x1.45mm

Connections:
+3V3: C43.1, C44.1, C46.1, L5.1, R54.1, R57.1, TP16.1, U9.12 (VOUT), U9.13 (VOUT), U9.14 (VOUT), U10.1 (EN), U10.8 (VIN)
+5V: C45.1, TP15.1, U10.4 (VOUT)
ARX: D12.2 (A)
ESP: D9.2 (A)
GND: C40.2, C41.2, C42.2, C43.2, C44.2, C45.2, C46.2, R49.2, R50.2, R52.2, R53.2, R56.1, R58.2, U8.8 (GND), U9.2 (PGND), U9.9 (AGND), U10.6 (PGND), U10.7 (SGND), U10.9 (EP)
MSC: D8.2 (A)
unnamed: C40.1, U8.10 (ITIMER)
unnamed: C41.1, U8.7 (DVDT)
unnamed: L4.1, U9.3 (L1)
unnamed: L4.2, U9.1 (L2)
unnamed: L5.2, U10.5 (SW)
unnamed: R48.2, R49.1, U8.1 (EN/UVLO)
unnamed: R50.1, U8.9 (ILM)
unnamed: R51.2, R52.1, U8.4 (PGTH)
unnamed: R53.1, U8.2 (OVCSEL)
unnamed: R54.2, TP12.1, U8.3 (PG)
unnamed: R55.1, R56.2, U9.10 (PFM/PWM)
unnamed: R57.2, R58.1, U9.11 (FB)
unnamed: TP14.1, U10.3 (PG)
PXH: D10.2 (A)
USB: D11.2 (A)
VBUS_EFUSE: C42.1, R51.1, R55.2, TP13.1, U8.6 (OUT), U9.4 (VIN), U9.5 (VIN), U9.6 (VIN), U9.7 (VINA), U9.8 (EN)
VBUS_PIN: D8.1 (K), D9.1 (K), D10.1 (K), D11.1 (K), D12.1 (K), R48.1, TP11.1, U8.5 (IN)

Notes on the sheet:
Main 3V3 power circuitry
Auxiliary 5V boost circuitry
Power inputs multiplexer
PWM - high PFM - low
