septentrio-gnss/mowi/mowi/subsys_usb.sch

## KiCad design mowi/subsys_usb.sch (2021-09-22)

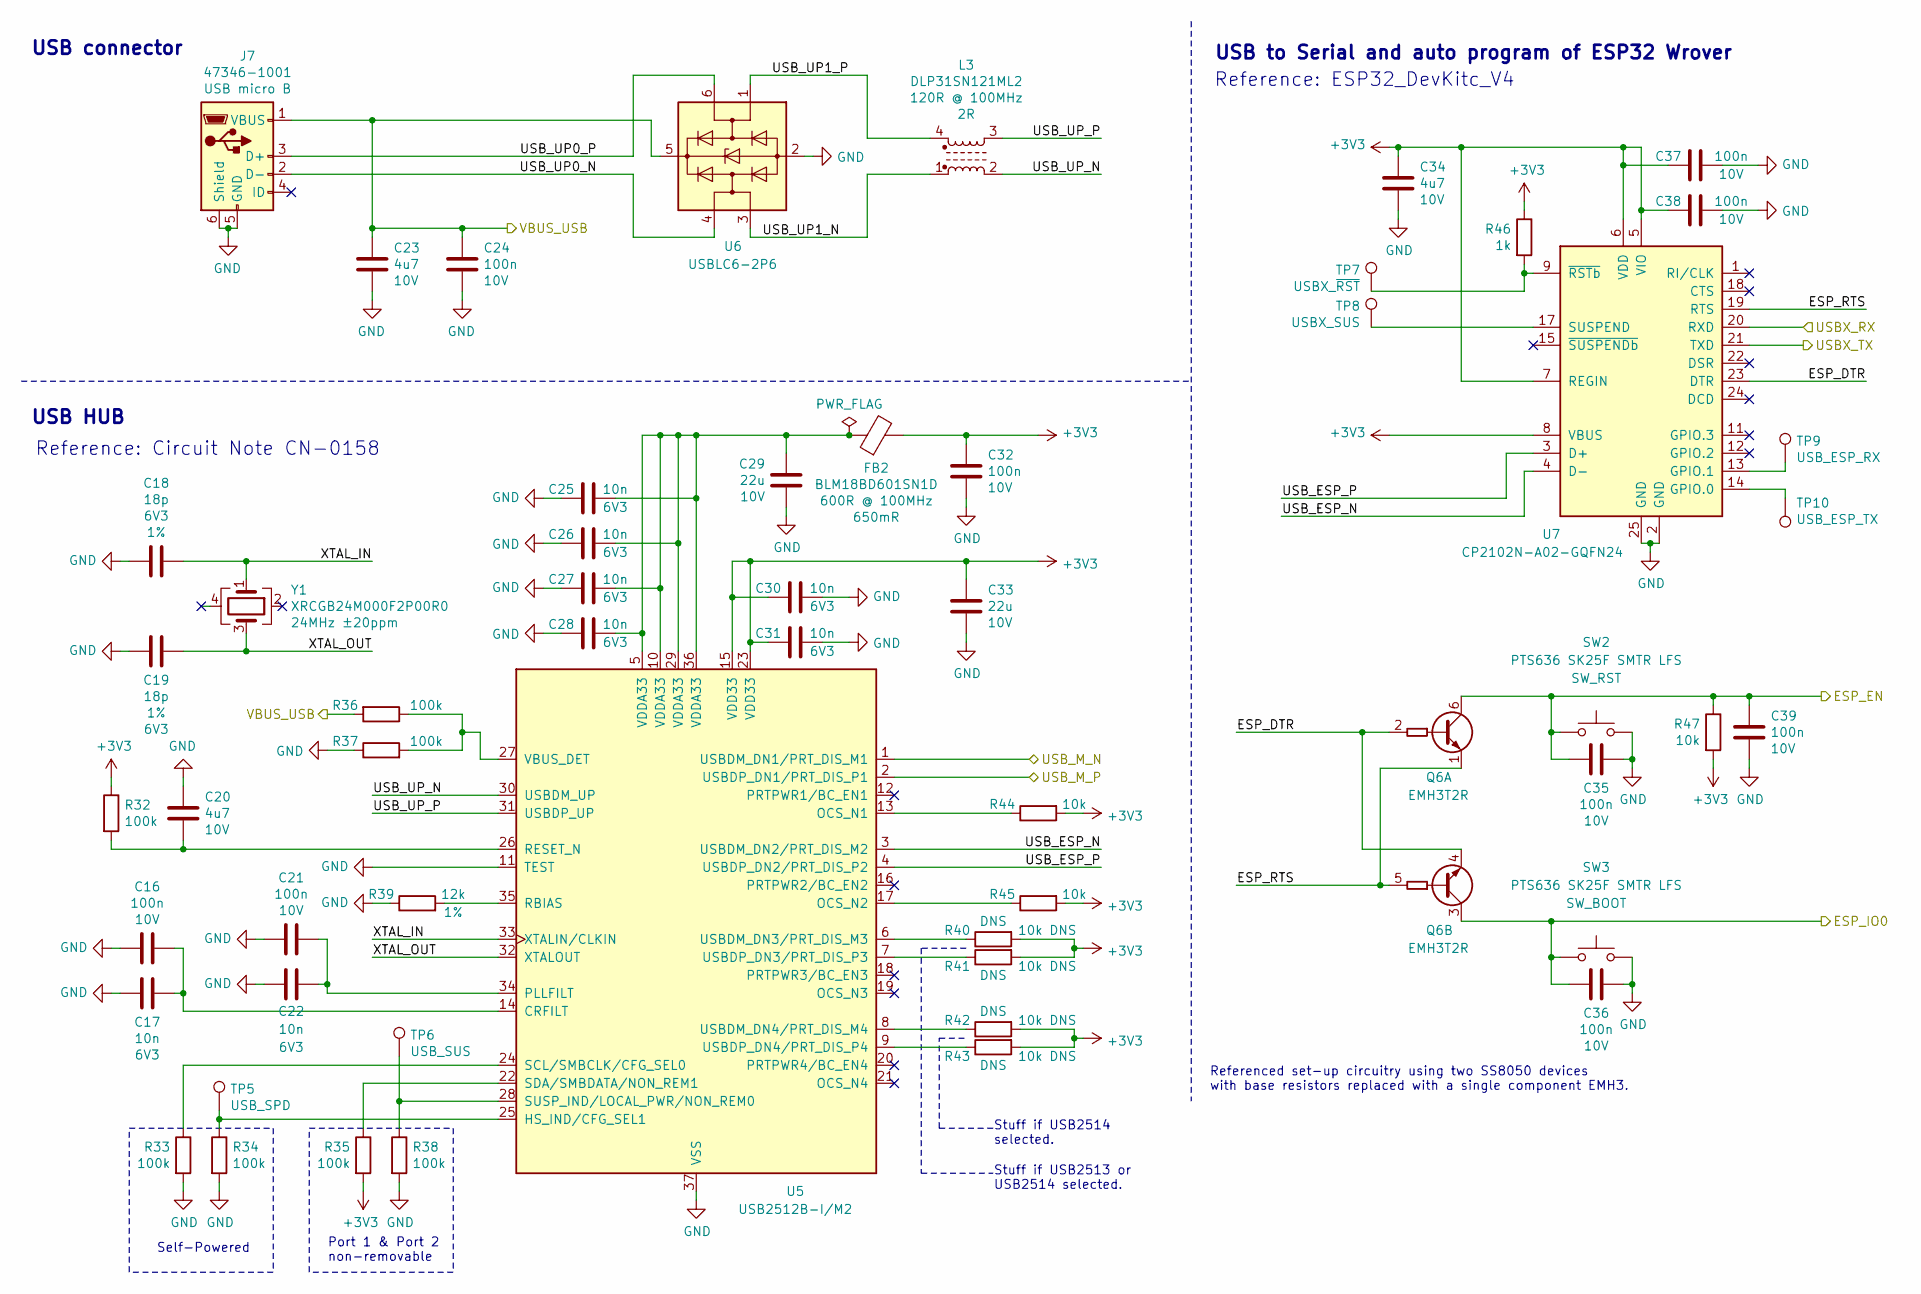
[picture p50: schematic subsys_usb.sch]

Parts:
C16, C21, C24, C32, C35, C36, C37, C38, C39: 100n; C_0402_1005Metric; Voltage 10V
C17, C22, C25, C26, C27, C28, C30, C31: 10n; C_0402_1005Metric; Voltage 6V3
C18: 18p; C_0201_0603Metric; Voltage 6V3; Tolerance 1%
C19: 18p; C_0201_0603Metric; Tolerance 1%; Voltage 6V3
C20, C23, C34: 4u7; C_0603_1608Metric; Voltage 10V
C29, C33: 22u; C_0805_2012Metric; Voltage 10V
FB2: BLM18BD601SN1D; L_0603_1608Metric
J7: 47346-1001; USB_Micro-B_Molex_47346-0001
L3: DLP31SN121ML2; L_Choke_Murata_DLP31SNxxxML2_3.2x1.6x1.15mm
Q6: EMH3T2R; SOT-563
R32, R33, R34, R35, R36, R37, R38: 100k; R_0402_1005Metric
R39: 12k; R_0402_1005Metric; Tolerance 1%
R40, R41, R42, R43: 10k DNS; R_0402_1005Metric
R44, R45, R47: 10k; R_0402_1005Metric
R46: 1k; R_0402_1005Metric
SW2, SW3: PTS636 SK25F SMTR LFS; SW_SPST_PTS636-SK25F_6.0x3.5x2.5mm_250gf
TP5: USB_SPD; TestPoint_Pad_D1.0mm
TP6: USB_SUS; TestPoint_Pad_D1.0mm
TP7: USBX_~RST; TestPoint_Pad_D1.0mm
TP8: USBX_SUS; TestPoint_Pad_D1.0mm
TP9: USB_ESP_RX; TestPoint_Pad_D1.0mm
TP10: USB_ESP_TX; TestPoint_Pad_D1.0mm
U5: USB2512B-I/M2; Microchip_QFN-36-1EP_6x6mm_P0.5mm_EP3.7x3.7mm
U6: USBLC6-2P6; ST_SOT-666_1.6x1.2x0.5mm
U7: CP2102N-A02-GQFN24; QFN-24-1EP_4x4mm_P0.5mm_EP2.6x2.6mm_ThermalVias
Y1: XRCGB24M000F2P00R0; Crystal_Murata_XRCGB_2.0x1.6x0.65mm

Connections:
+3V3: C30.1, C31.1, C32.1, C33.1, C34.1, C37.1, C38.1, FB2.2, R32.1, R35.2, R40.2, R41.2, R42.2, R43.2, R44.2, R45.2, R46.1, R47.2, U5.15 (VDD33), U5.23 (VDD33), U7.5 (VIO), U7.6 (VDD), U7.7 (REGIN), U7.8 (VBUS)
ESP_DTR: Q6.2 (B1), Q6.4 (E2), U7.23 (DTR)
ESP_EN: C35.1, C39.1, Q6.6 (C1), R47.1, SW2.1
ESP_IO0: C36.1, Q6.3 (C2), SW3.1
ESP_RTS: Q6.1 (E1), Q6.5 (B2), U7.19 (RTS)
GND: C16.2, C17.2, C18.2, C19.2, C20.2, C21.2, C22.2, C23.1, C24.1, C25.2, C26.2, C27.2, C28.2, C29.2, C30.2, C31.2, C32.2, C33.2, C34.2, C35.2, C36.2, C37.2, C38.2, C39.2, J7.5 (GND), J7.6 (Shield), R33.2, R34.2, R37.1, R38.2, R39.1, SW2.2, SW3.2, U5.11 (TEST), U5.37 (VSS), U6.2 (GND), U7.2 (GND), U7.25 (GND)
unnamed: C16.1, C17.1, U5.14 (CRFILT)
unnamed: C20.1, R32.2, U5.26 (RESET_N)
unnamed: C21.1, C22.1, U5.34 (PLLFILT)
unnamed: C25.1, C26.1, C27.1, C28.1, C29.1, FB2.1, U5.5 (VDDA33), U5.10 (VDDA33), U5.29 (VDDA33), U5.36 (VDDA33)
unnamed: R33.1, U5.24 (SCL/SMBCLK/CFG_SEL0)
unnamed: R34.1, TP5.1, U5.25 (HS_IND/CFG_SEL1)
unnamed: R35.1, U5.22 (SDA/SMBDATA/NON_REM1)
unnamed: R36.1, R37.2, U5.27 (VBUS_DET)
unnamed: R38.1, TP6.1, U5.28 (SUSP_IND/LOCAL_PWR/NON_REM0)
unnamed: R39.2, U5.35 (RBIAS)
unnamed: R40.1, U5.6 (USBDM_DN3/PRT_DIS_M3)
unnamed: R41.1, U5.7 (USBDP_DN3/PRT_DIS_P3)
unnamed: R42.1, U5.8 (USBDM_DN4/PRT_DIS_M4)
unnamed: R43.1, U5.9 (USBDP_DN4/PRT_DIS_P4)
unnamed: R44.1, U5.13 (OCS_N1)
unnamed: R45.1, U5.17 (OCS_N2)
unnamed: R46.2, TP7.1, U7.9 (~RSTb)
unnamed: TP8.1, U7.17 (SUSPEND)
unnamed: TP9.1, U7.13 (GPIO.1)
unnamed: TP10.1, U7.14 (GPIO.0)
USBX_RX: U7.20 (RXD)
USBX_TX: U7.21 (TXD)
USB_ESP_N: U5.3 (USBDM_DN2/PRT_DIS_M2), U7.4 (D-)
USB_ESP_P: U5.4 (USBDP_DN2/PRT_DIS_P2), U7.3 (D+)
USB_M_N: U5.1 (USBDM_DN1/PRT_DIS_M1)
USB_M_P: U5.2 (USBDP_DN1/PRT_DIS_P1)
USB_UP0_N: J7.2 (D-), U6.4 (I/O2)
USB_UP0_P: J7.3 (D+), U6.6 (I/O1)
USB_UP1_N: L3.1, U6.3 (I/O2)
USB_UP1_P: L3.4, U6.1 (I/O1)
USB_UP_N: L3.2, U5.30 (USBDM_UP)
USB_UP_P: L3.3, U5.31 (USBDP_UP)
VBUS_USB: C23.2, C24.2, J7.1 (VBUS), R36.2, U6.5 (VBUS)
XTAL_IN: C18.1, U5.33 (XTALIN/CLKIN), Y1.1
XTAL_OUT: C19.1, U5.32 (XTALOUT), Y1.3

Notes on the sheet:
USB HUB
USB to Serial and auto program of ESP32 Wrover
Reference: ESP32_DevKitc_V4
Stuff if USB2514 selected.
USB connector
Reference: Circuit Note CN-0158
Self-Powered
Port 1 & Port 2 non-removable
Referenced set-up circuitry using two SS8050 devices with base resistors replaced with a single component EMH3.
Stuff if USB2513 or USB2514 selected.
